Rhetticle/DGAS/Photos/about.jpeg

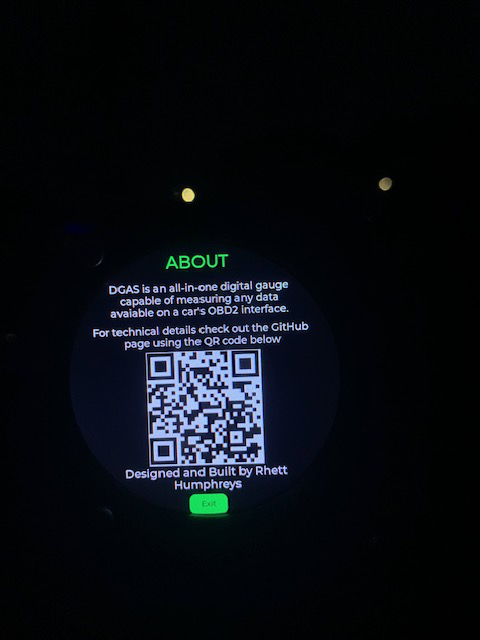
Photos/about.jpeg
