Rhetticle/DGAS/Photos/Boost.jpeg

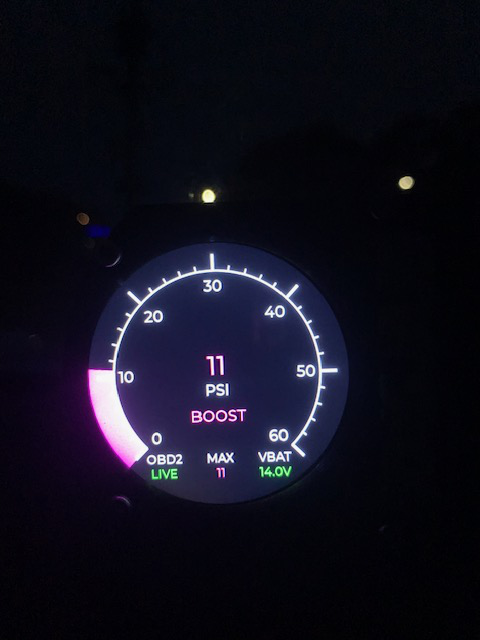
Photos/Boost.jpeg
