Rhetticle/DGAS/Photos/coolant.jpeg

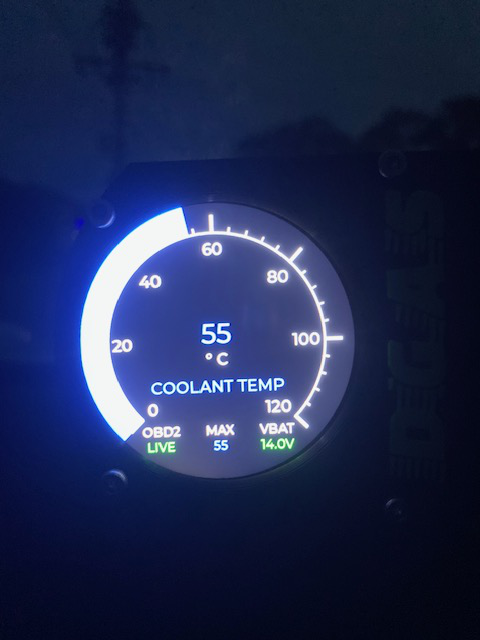
Photos/coolant.jpeg
