Rhetticle/DGAS/Photos/dgas back internal.jpeg

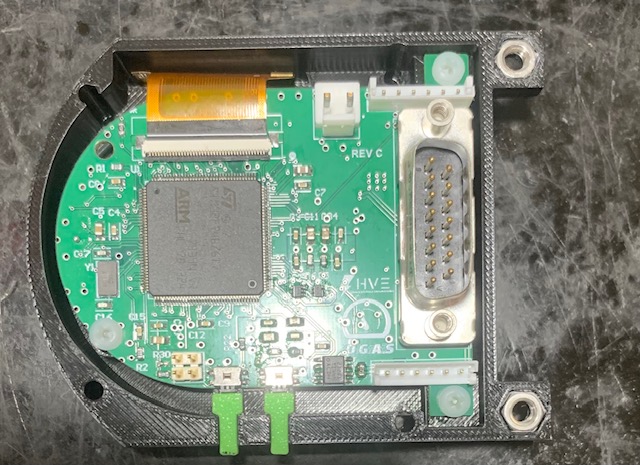
Photos/dgas back internal.jpeg
