Rhetticle/DGAS/Photos/dgas back.jpeg

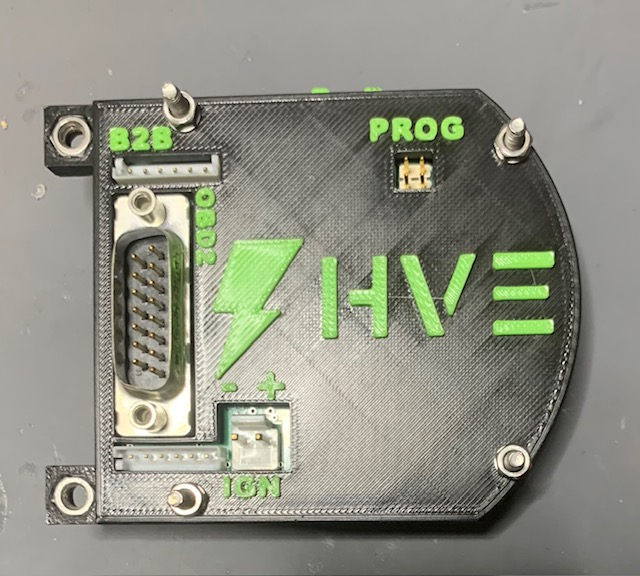
Photos/dgas back.jpeg
