Rhetticle/DGAS/Photos/dgas front.jpeg

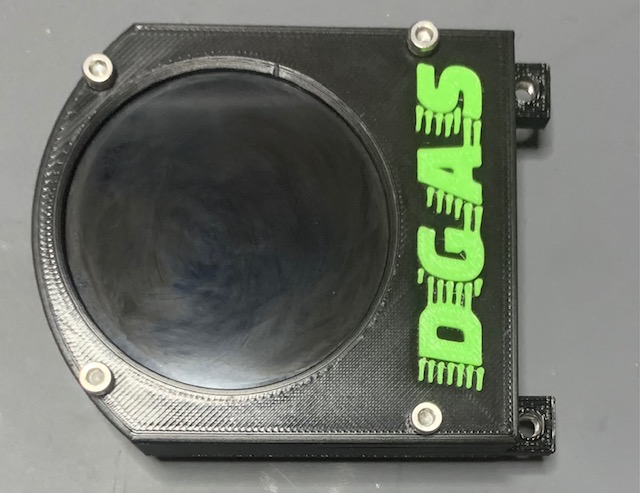
Photos/dgas front.jpeg
