Rhetticle/DGAS/Photos/dgas.jpeg

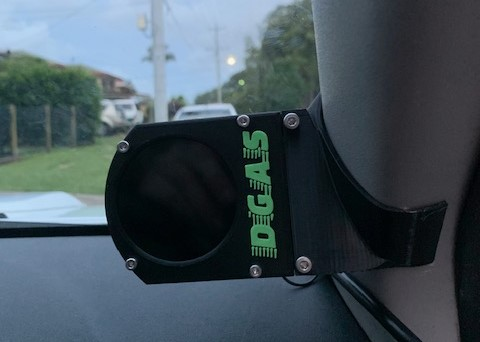
Photos/dgas.jpeg
