Rhetticle/DGAS/Photos/engine spped.jpeg

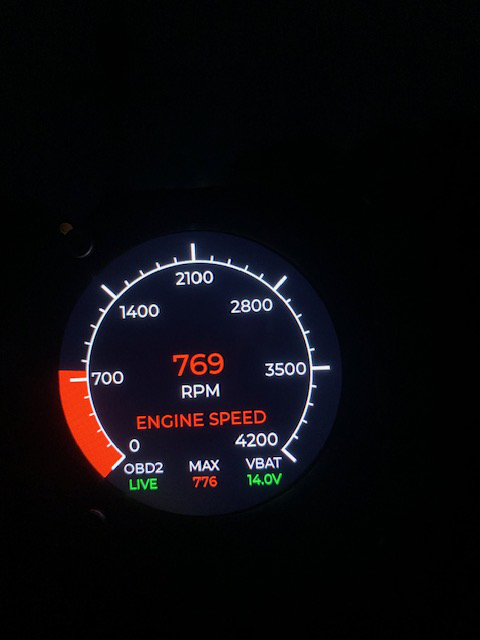
Photos/engine spped.jpeg
