Rhetticle/DGAS/Photos/MAF.jpeg

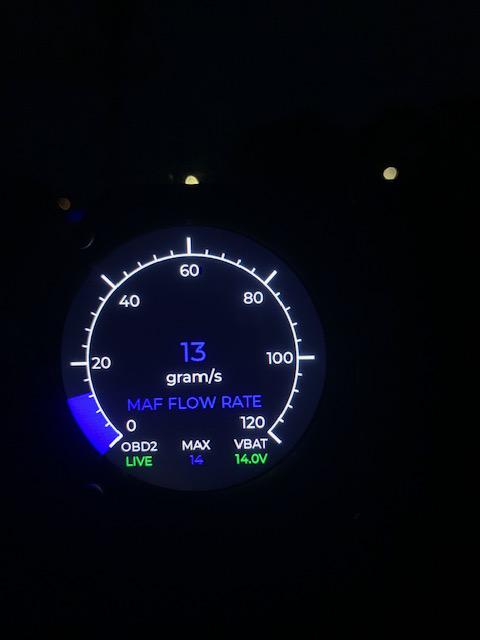
Photos/MAF.jpeg
