Rhetticle/DGAS/Photos/menu.jpeg

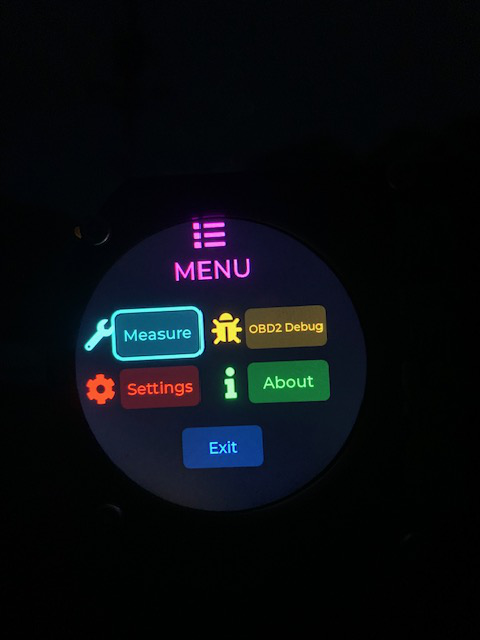
Photos/menu.jpeg
