Rhetticle/DGAS/Photos/pcb 3d.png

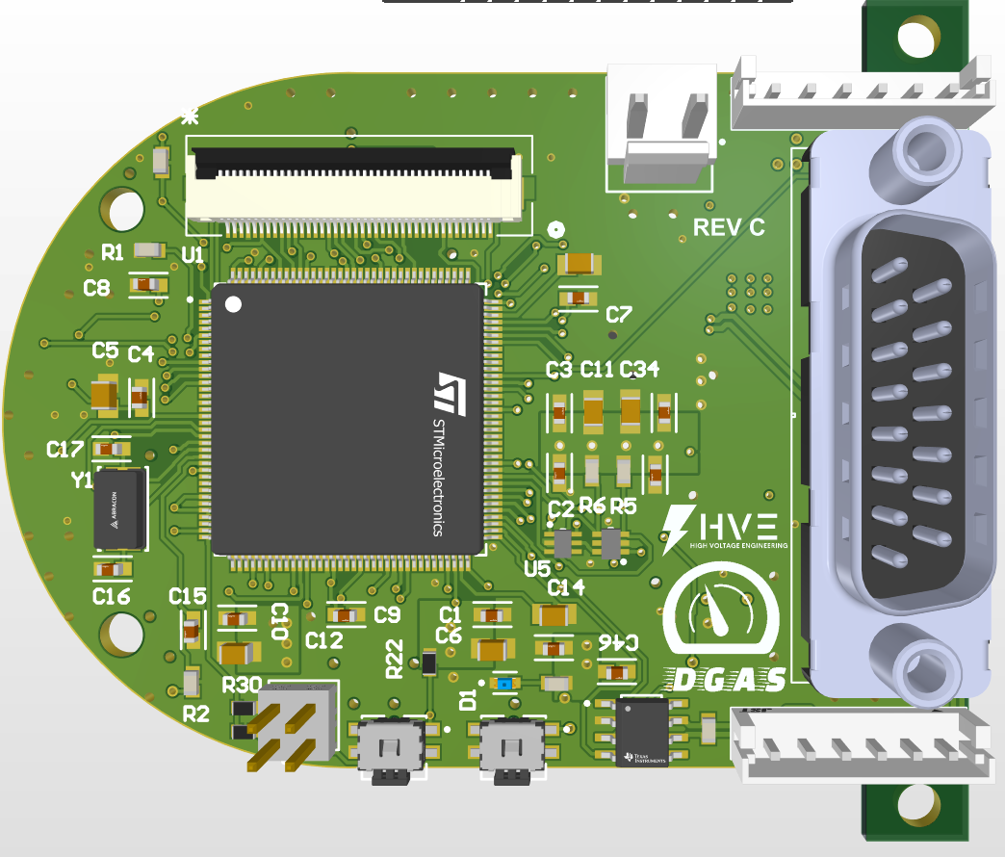
Photos/pcb 3d.png
