Rhetticle/DGAS/DGAS Firmware/Core/Inc/OBD2.h

/*
 * OBD2.h
 *
 *  Created on: Jan 11, 2025
 *      Author: rhett
 */

#ifndef INC_OBD2_H_
#define INC_OBD2_H_

#include <stm32f7xx.h>
#include <stdbool.h>

typedef enum {
	OBD_ERROR,
	OBD_INIT,
	OBD_LIVE,
	OBD_TIMEOUT,
} OBDBusStatus;

typedef enum {
	BUS_ID_KWP,
	BUS_ID_9141,
	BUS_ID_CAN,
	BUS_ID_AUTO,
} BusID;

typedef struct {
	OBDBusStatus status;
	HAL_StatusTypeDef (*init_bus)(void);
	HAL_StatusTypeDef (*get_pid)(uint8_t, uint8_t*);
	HAL_StatusTypeDef (*get_dtcs)(uint8_t*);
	HAL_StatusTypeDef (*clear_dtcs)(void);
	BusID id;
}OBDBus;


#define CONV_KPA_TO_PSI(x) (x * 0.145)

#define DBG_MSG_MAX_SIZE 256

#define OBD2_DATA_MAX 4 // maximum of four bytes sent in OBD2 response

#define OBD2_MODE_LIVE 0x01
#define OBD2_MODE_DTC 0x03
#define OBD2_MODE_KWP_DTC 0x13 // for some reason dtc mode is 0x13 for KWP
#define OBD2_MODE_CLEAR_DTC 0x04
#define OBD_RESPONSE_MODE_OFFSET 0x40
#define OBD_DTC_MAX_COUNT 255

#define OBD2_PID_SUPPORTED_PIDS 0x00
#define OBD2_PID_RPM 0x0C
#define OBD2_PID_VEHICLE_SPEED 0x0D
#define OBD2_PID_ENG_LOAD 0x04
#define OBD2_PID_COOLANT_TEMP 0x05
#define OBD2_PID_THROTTLE_POS 0x11
#define OBD2_PID_INTAKE_TEMP 0x0F
#define OBD2_PID_MAF_FLOW_RATE 0x10
#define OBD2_PID_MANIFOLD_PRESSURE 0x0B
#define OBD2_PID_FUEL_PRESSURE_MANIFOLD_RELATIVE 0x22
#define OBD2_PID_FUEL_PRESSURE 0x23

HAL_StatusTypeDef obd2_get_pid(OBDBus* bus, uint8_t pid, uint8_t* response);
HAL_StatusTypeDef obd2_get_dtcs(OBDBus* bus, uint8_t* response);
HAL_StatusTypeDef obd2_clear_dtcs(OBDBus* bus);
HAL_StatusTypeDef obd2_get_rpm(OBDBus* bus, uint16_t* rpm);
HAL_StatusTypeDef obd2_get_engine_load(OBDBus* bus, uint16_t* load);
HAL_StatusTypeDef obd2_get_vehicle_speed(OBDBus* bus, uint16_t* speed);
HAL_StatusTypeDef obd2_get_coolant_temp(OBDBus* bus, uint16_t* temp);
HAL_StatusTypeDef obd2_get_throttle_pos(OBDBus* bus, uint16_t* pos);
HAL_StatusTypeDef obd2_get_intake_temp(OBDBus* bus, uint16_t* temp);
HAL_StatusTypeDef obd2_get_maf_flow_rate(OBDBus* bus, uint16_t* flowRate);
HAL_StatusTypeDef obd2_get_boost(OBDBus* bus, uint16_t* boost);
HAL_StatusTypeDef obd2_get_fuel_pressure(OBDBus* bus, uint16_t* pressure);
HAL_StatusTypeDef obd2_get_fuel_pressure_manifold_relative(OBDBus* bus, uint16_t* pressure);
HAL_StatusTypeDef obd2_dummy_request(OBDBus* bus);
void init_bus_struct_from_id(OBDBus* bus, BusID id);
HAL_StatusTypeDef obd2_bus_auto_detect(OBDBus* bus);
#endif /* INC_OBD2_H_ */
